stiamon77/PC-Mini-Box-v4-24ssd-2.5-NAS/For laser cutting/RAID 2 3mm.dxf

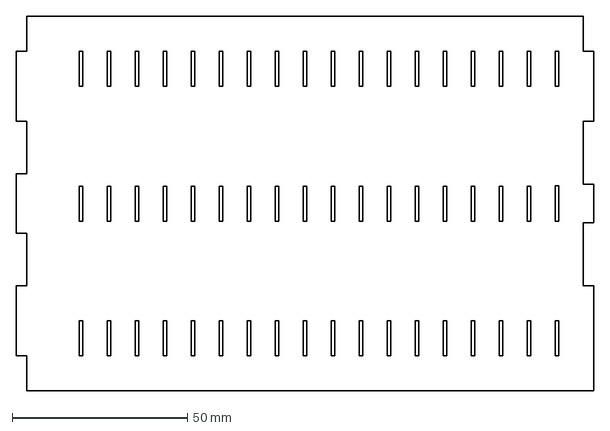
[picture p25: CAD file, 2024-06-26]
For laser cutting/RAID 2 3mm.dxf
165.0 x 107.0 mm
