stiamon77/PC-Mini-Box-v4-24ssd-2.5-NAS/For laser cutting/Decorative element 2-2 3mm.dxf

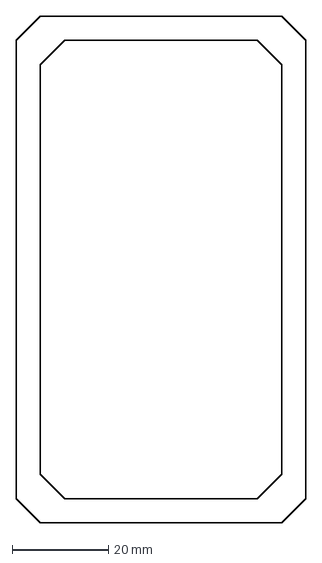
[picture p26: CAD file, 2024-06-26]
For laser cutting/Decorative element 2-2 3mm.dxf
60.0 x 105.0 mm
