stiamon77/PC-Mini-Box-v4-24ssd-2.5-NAS/For laser cutting/Decorative element 2-1 3mm.dxf

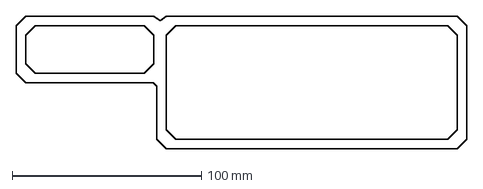
[picture p27: CAD file, 2024-06-26]
For laser cutting/Decorative element 2-1 3mm.dxf
237.7 x 70.0 mm
