stiamon77/PC-Mini-Box-v4-24ssd-2.5-NAS/For laser cutting/Connector 3mm.dxf

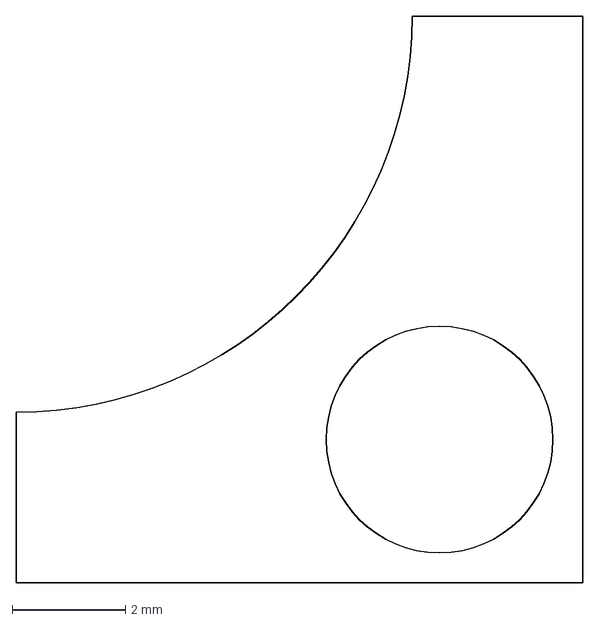
[picture p28: CAD file, 2024-06-26]
For laser cutting/Connector 3mm.dxf
10.0 x 10.0 mm
