stiamon77/PC-Mini-Box-v4-24ssd-2.5-NAS/For laser cutting/RAID 4 3mm.dxf

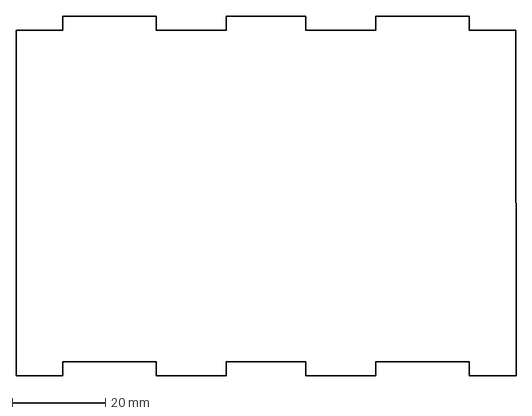
[picture p29: CAD file, 2024-06-26]
For laser cutting/RAID 4 3mm.dxf
107.0 x 77.0 mm
