stiamon77/PC-Mini-Box-v4-24ssd-2.5-NAS/For laser cutting/RAID 1 3mm.dxf

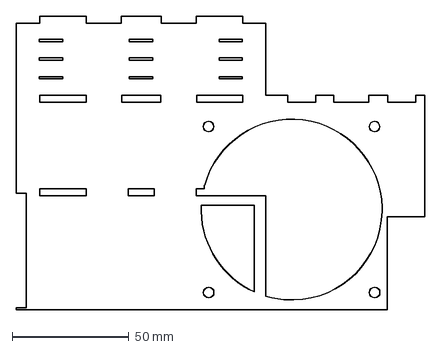
[picture p30: CAD file, 2024-06-26]
For laser cutting/RAID 1 3mm.dxf
175.0 x 126.0 mm
