stiamon77/PC-Mini-Box-v4-24ssd-2.5-NAS/For laser cutting/Bottom cover 5mm.dxf

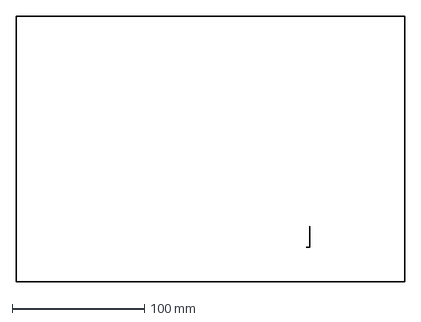
[picture p31: CAD file, 2024-06-26]
For laser cutting/Bottom cover 5mm.dxf
294.0 x 201.0 mm
